samnov17/RedBot_autonomous_robot_smartcity/Photo/1 (1).jpg

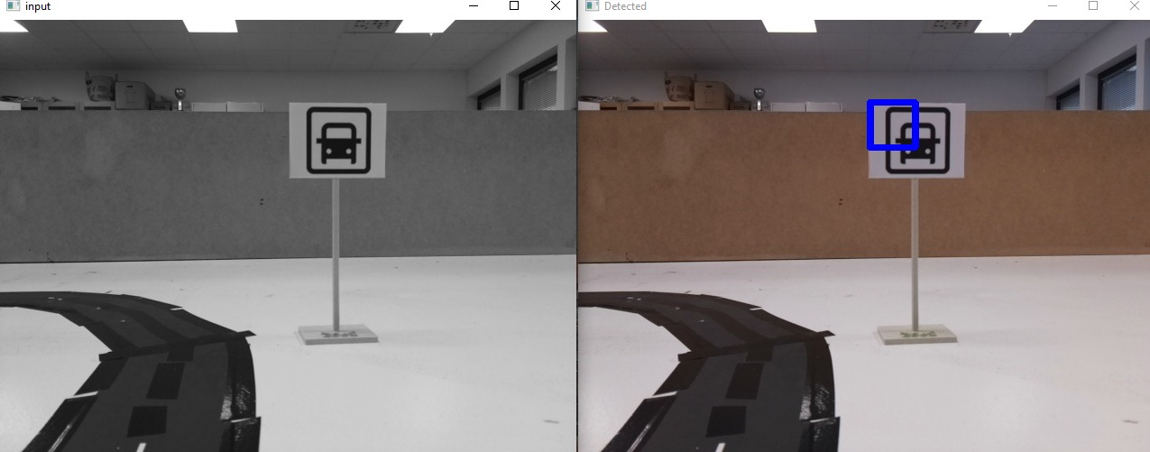
Photo/1 (1).jpg
