samnov17/RedBot_autonomous_robot_smartcity/Photo/1 (2).jpg

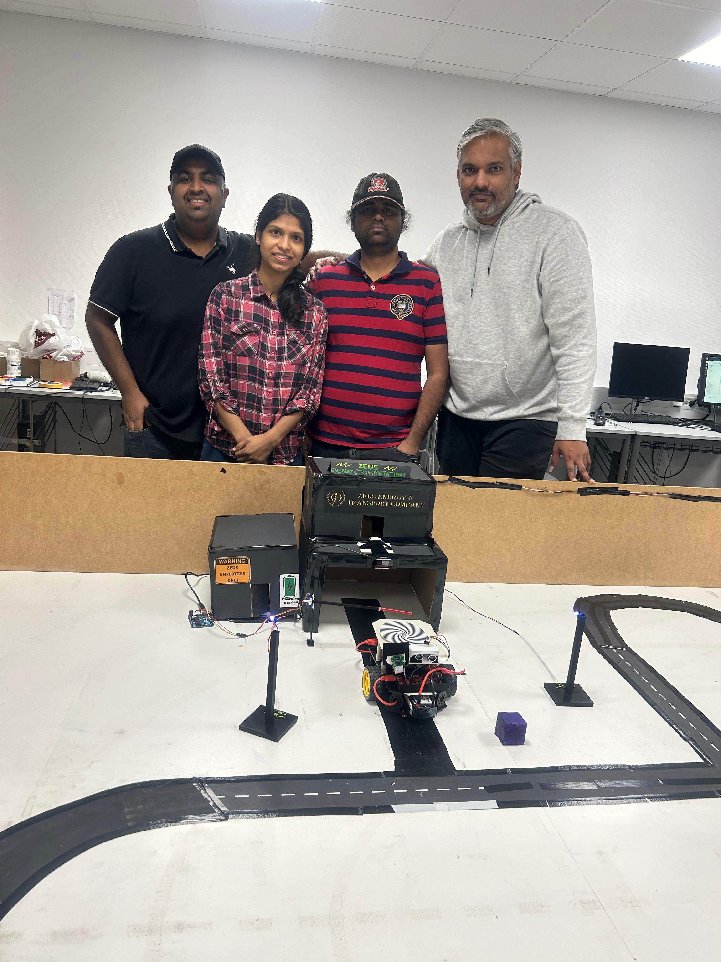
Photo/1 (2).jpg
