samnov17/RedBot_autonomous_robot_smartcity/Photo/1 (7).jpg

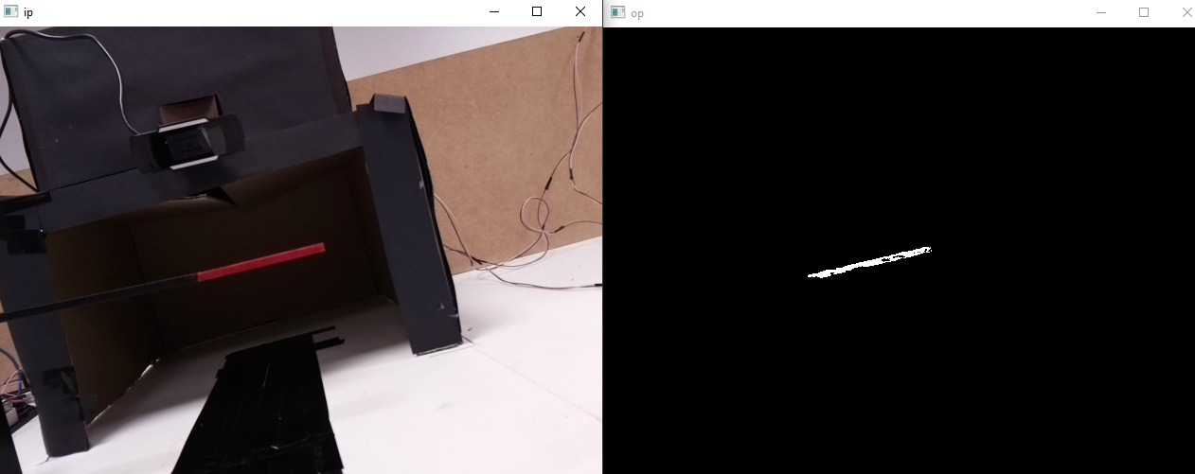
Photo/1 (7).jpg
