samnov17/RedBot_autonomous_robot_smartcity/Photo/1 (9).jpg

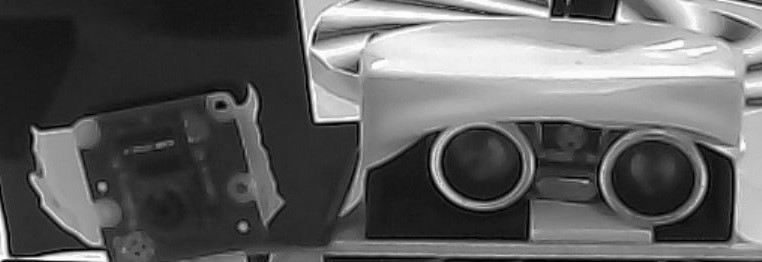
Photo/1 (9).jpg
